jackbrad1ey/thingamaboard/cad/pcb/kailh_choc_switch.SLDPRT

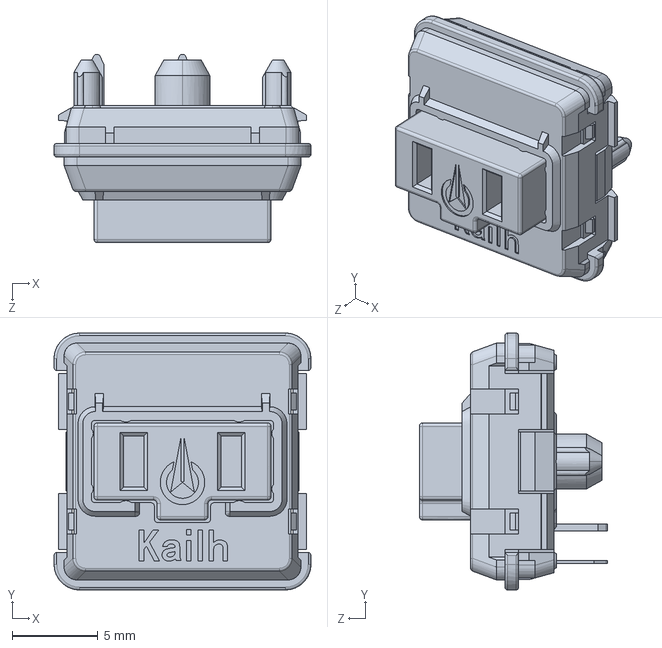
[picture p24: CAD file, 2023-06-26]
cad/pcb/kailh_choc_switch.SLDPRT
15.0 x 15.0 x 11.0 mm
