jackbrad1ey/thingamaboard/cad/pcb/female_1x4_2.54mm_header.SLDPRT

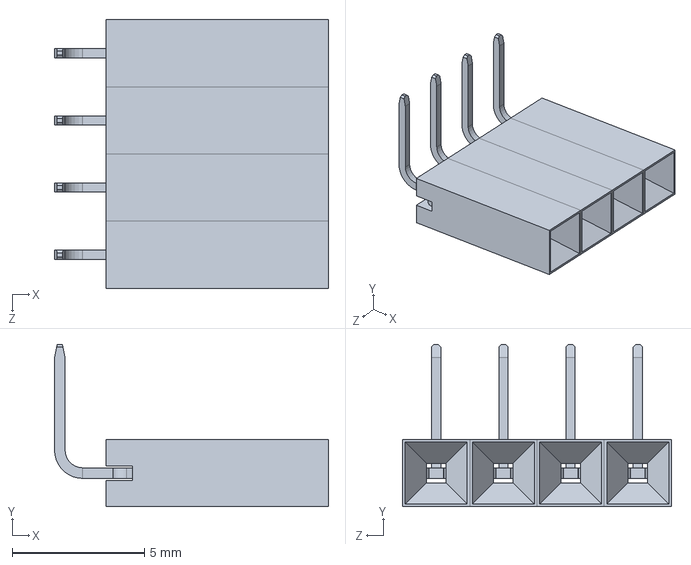
[picture p25: CAD file, 2023-06-26]
cad/pcb/female_1x4_2.54mm_header.SLDPRT
10.4 x 6.14 x 10.2 mm
