jackbrad1ey/thingamaboard/cad/case/M2_screws.SLDPRT

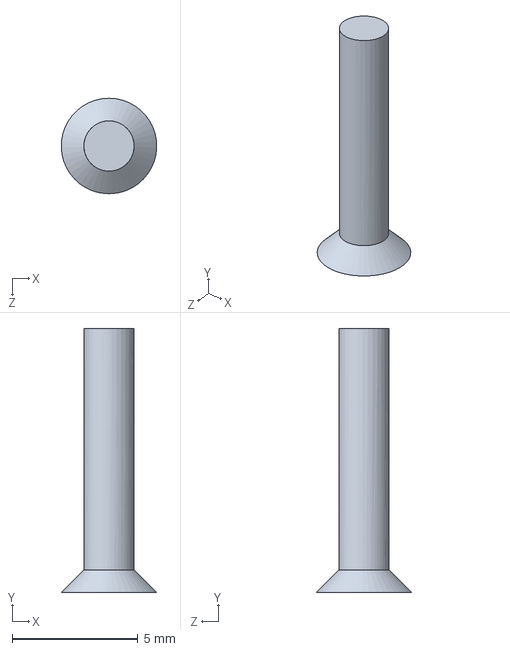
[picture p26: CAD file, 2023-10-28]
cad/case/M2_screws.SLDPRT
3.80 x 10.5 x 3.80 mm
